thainnos/LICSTER/images/fischertechnik_lowres.png

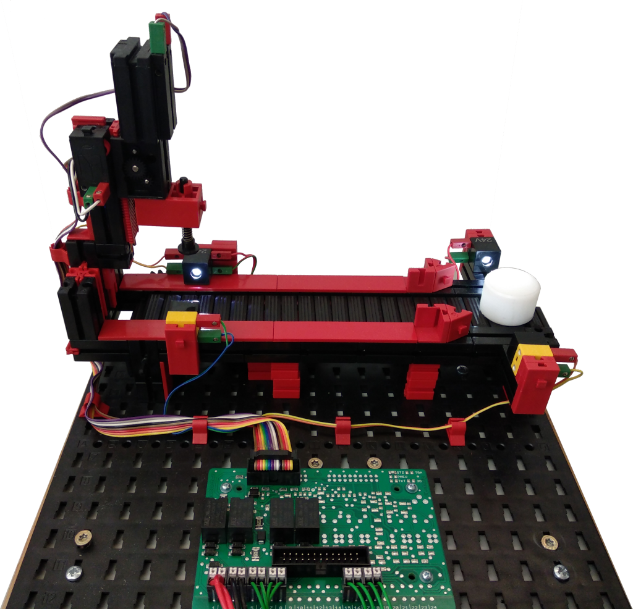
images/fischertechnik_lowres.png
