thainnos/LICSTER/projects/IntrusionDetectionSystem/images/costum-rules.PNG

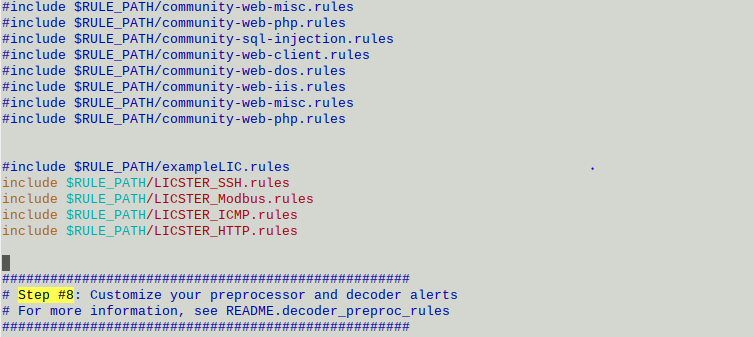
projects/IntrusionDetectionSystem/images/costum-rules.PNG
