thainnos/LICSTER/devices/remote_io/software/Inc/colors.h

#ifndef _COLORS_
#define _COLORS_

/* Foreground Colors in Console
 * Does only work, if console supports
 * colors
 * */
#define CRST  "\x1B[0m"
#define CRED  "\x1B[31m"
#define CGRN  "\x1B[32m"
#define CYEL  "\x1B[33m"
#define CBLU  "\x1B[34m"
#define CMAG  "\x1B[35m"
#define CCYN  "\x1B[36m"
#define CWHT  "\x1B[37m"

#endif  /* _COLORS_ */
