thainnos/LICSTER/devices/remote_io/software/Inc/global.h

#ifndef _GLOBAL_
#define _GLOBAL_

/* Scan Parameters Defines */
#define IPRANGE 255 //TODO 255
#define MAXPORTS 10
#define SCANDELAY 60000

#define LOGLEN 196    // Characters of Log Messages

#endif  /* _GLOBAL_ */
