thainnos/LICSTER/devices/hmi/software/tests/test_db.py

import sqlite3

import pytest
from app.db import get_db


def test_get_close_db(app):
    """
    Tests if get_db returns the same connection each time it's
    called and if the connection is closed after executing a
    statement.
    """
    with app.app_context():
        db = get_db()
        assert db is get_db()

    with pytest.raises(sqlite3.ProgrammingError) as e:
        db.execute('SELECT 1')

    assert 'closed' in str(e.value)


def test_init_db_command(runner, monkeypatch):
    class Recorder(object):
        called = False

    def fake_init_db():
        Recorder.called = True

    monkeypatch.setattr('app.db.init_db', fake_init_db)
    result = runner.invoke(args=['init-db'])
    assert 'Initialized' in result.output
    assert Recorder.called
